diablo4338/water_cooling_controller/firmware/src/metrics/ads1115.c

#include "ads1115.h"

#include <math.h>
#include <string.h>

#include "esp_err.h"
#include "esp_log.h"
#include "esp_timer.h"
#include "freertos/FreeRTOS.h"
#include "freertos/task.h"
#include "driver/i2c_master.h"
#include "shared_i2c_bus.h"

static const char *ADS_TAG = "ads1115";
static bool s_i2c_inited = false;
static bool s_started = false;
static i2c_master_bus_handle_t s_i2c_bus = NULL;
static i2c_master_dev_handle_t s_i2c_dev = NULL;
static i2c_device_config_t s_dev_cfg = {0};
static bool s_ads_error = false;
static int64_t s_retry_after_us = 0;

#define ADS1115_REG_CONVERSION 0x00
#define ADS1115_REG_CONFIG     0x01

#define ADS1115_CFG_OS_SINGLE   (1U << 15)
#define ADS1115_CFG_MUX_SHIFT   12
#define ADS1115_CFG_PGA_SHIFT   9
#define ADS1115_CFG_MODE_SINGLE (1U << 8)
#define ADS1115_CFG_DR_SHIFT    5
#define ADS1115_CFG_COMP_QUE    0x0003

#define ADS1115_I2C_TIMEOUT_MS 100
#define ADS1115_RETRY_COOLDOWN_US (1000 * 1000LL)

static uint16_t ads1115_build_config(uint8_t channel) {
    uint16_t mux = (uint16_t)(0x4 + (channel & 0x03)) << ADS1115_CFG_MUX_SHIFT;
    uint16_t pga = (uint16_t)0x1 << ADS1115_CFG_PGA_SHIFT;  // ±4.096V
    uint16_t dr = (uint16_t)0x4 << ADS1115_CFG_DR_SHIFT;    // 128 SPS
    return (uint16_t)(ADS1115_CFG_OS_SINGLE | mux | pga | ADS1115_CFG_MODE_SINGLE | dr | ADS1115_CFG_COMP_QUE);
}

static void ads1115_fill_dev_cfg(void) {
    s_dev_cfg = (i2c_device_config_t) {
        .dev_addr_length = I2C_ADDR_BIT_LEN_7,
        .device_address = ADS1115_I2C_ADDR,
        .scl_speed_hz = ADS1115_I2C_FREQ_HZ,
        .scl_wait_us = 0,
        .flags = {
            .disable_ack_check = 0,
        },
    };
}

static bool ads1115_attach_device(void) {
    if (!s_i2c_bus) return false;
    if (s_i2c_dev) return true;
    if (s_dev_cfg.device_address == 0) {
        ads1115_fill_dev_cfg();
    }
    if (!shared_i2c_bus_lock(pdMS_TO_TICKS(ADS1115_I2C_TIMEOUT_MS))) {
        ESP_LOGW(ADS_TAG, "i2c add device lock timeout");
        s_ads_error = true;
        return false;
    }

    esp_err_t err = i2c_master_bus_add_device(s_i2c_bus, &s_dev_cfg, &s_i2c_dev);
    shared_i2c_bus_unlock();
    if (err != ESP_OK) {
        ESP_LOGW(ADS_TAG, "i2c add device err=%s", esp_err_to_name(err));
        s_ads_error = true;
        return false;
    }
    return true;
}

static void ads1115_recover(const char *stage, esp_err_t err) {
    ESP_LOGW(ADS_TAG, "%s err=%s", stage, esp_err_to_name(err));
    s_ads_error = true;
    s_retry_after_us = esp_timer_get_time() + ADS1115_RETRY_COOLDOWN_US;
    if (!s_i2c_bus) return;

    if (!shared_i2c_bus_lock(pdMS_TO_TICKS(ADS1115_I2C_TIMEOUT_MS))) {
        ESP_LOGW(ADS_TAG, "i2c reset lock timeout");
        return;
    }
    esp_err_t reset_err = i2c_master_bus_reset(s_i2c_bus);
    shared_i2c_bus_unlock();
    if (reset_err != ESP_OK) {
        ESP_LOGW(ADS_TAG, "i2c bus reset err=%s", esp_err_to_name(reset_err));
    }
}

bool ads1115_init(void) {
    if (s_started && !s_ads_error && s_i2c_dev != NULL) return true;

    if (s_started) {
        ESP_LOGW(ADS_TAG, "reinitializing after ADS/I2C error");
    }

    s_i2c_bus = shared_i2c_bus_get_handle();
    if (s_i2c_bus == NULL) {
        ESP_LOGW(ADS_TAG, "shared i2c bus is not initialized");
        s_ads_error = true;
        return false;
    }

    if (s_dev_cfg.device_address == 0) {
        ads1115_fill_dev_cfg();
    }
    if (!ads1115_attach_device()) return false;

    s_i2c_inited = true;
    s_started = true;
    s_ads_error = false;
    s_retry_after_us = 0;
    return true;
}

bool ads1115_read_raw(uint8_t channel, int16_t *out_raw) {
    if (!out_raw || channel > 3) return false;
    if (s_ads_error) {
        int64_t now_us = esp_timer_get_time();
        if (now_us < s_retry_after_us) return false;
    }
    if ((!s_started || s_ads_error || !s_i2c_dev) && !ads1115_init()) {
        return false;
    }
    if (!s_i2c_dev) return false;

    uint16_t cfg = ads1115_build_config(channel);
    uint8_t buf[3] = {
        ADS1115_REG_CONFIG,
        (uint8_t)(cfg >> 8),
        (uint8_t)(cfg & 0xFF),
    };
    uint8_t reg = ADS1115_REG_CONVERSION;
    uint8_t data[2] = {0};

    // The first single-shot after changing MUX can still reflect the previous
    // input. Trigger and discard one conversion, then read the second one.
    for (int pass = 0; pass < 2; pass++) {
        if (!shared_i2c_bus_lock(pdMS_TO_TICKS(ADS1115_I2C_TIMEOUT_MS))) {
            ESP_LOGW(ADS_TAG, "i2c write cfg lock timeout");
            s_ads_error = true;
            return false;
        }
        esp_err_t err = i2c_master_transmit(
            s_i2c_dev, buf, sizeof(buf), ADS1115_I2C_TIMEOUT_MS);
        shared_i2c_bus_unlock();
        if (err != ESP_OK) {
            ads1115_recover("i2c write cfg", err);
            return false;
        }

        vTaskDelay(pdMS_TO_TICKS(ADS1115_CONV_DELAY_MS));

        if (!shared_i2c_bus_lock(pdMS_TO_TICKS(ADS1115_I2C_TIMEOUT_MS))) {
            ESP_LOGW(ADS_TAG, "i2c read conv lock timeout");
            s_ads_error = true;
            return false;
        }
        err = i2c_master_transmit_receive(
            s_i2c_dev, &reg, 1, data, sizeof(data), ADS1115_I2C_TIMEOUT_MS);
        shared_i2c_bus_unlock();
        if (err != ESP_OK) {
            ads1115_recover("i2c read conv", err);
            return false;
        }
    }

    *out_raw = (int16_t)((data[0] << 8) | data[1]);
    s_ads_error = false;
    return true;
}

bool ads1115_has_error(void) {
    return s_ads_error || (s_i2c_inited && s_i2c_dev == NULL);
}

float ads1115_raw_to_v(int16_t raw) {
    return ((float)raw * ADS1115_FS_V) / 32768.0f;
}

float ads1115_raw_to_temp(int16_t raw) {
    float volt_p = ads1115_raw_to_v(raw);
    if (volt_p <= 0.000001f) return NAN;

    float res_p = ((3.3f * 4700.0f) / volt_p) - 4700.0f;
    if (res_p <= 0.0f) return NAN;

    float inv_t = (1.0f / (25.0f + 273.15f)) + (logf(res_p / 10000.0f) / 3625.0f);
    float temp_c = (1.0f / inv_t) - 273.15f;
    return roundf(temp_c * 100.0f) / 100.0f;
}

#ifdef PAIR_RUN_TESTS
void ads1115_test_force_recoverable_error(void) {
    s_ads_error = true;
    s_started = true;
    s_retry_after_us = 0;
}
#endif
