diablo4338/water_cooling_controller/firmware/src/metrics/ads1115.h

#ifndef ADS1115_H
#define ADS1115_H

#include <stdbool.h>
#include <stdint.h>

#define ADS1115_I2C_ADDR      0x48
#define ADS1115_I2C_FREQ_HZ   400000

#define ADS1115_CONV_DELAY_MS     10
#define ADS1115_INTER_CH_DELAY_MS 5
#define ADS1115_FS_V              4.096f

bool ads1115_init(void);
bool ads1115_read_raw(uint8_t channel, int16_t *out_raw);
bool ads1115_has_error(void);
float ads1115_raw_to_v(int16_t raw);
float ads1115_raw_to_temp(int16_t raw);

#ifdef PAIR_RUN_TESTS
void ads1115_test_force_recoverable_error(void);
#endif

#endif
